ZouhirYachou/RPI5_RGsB_HAT/images/PXL_20260119_183532538.jpg

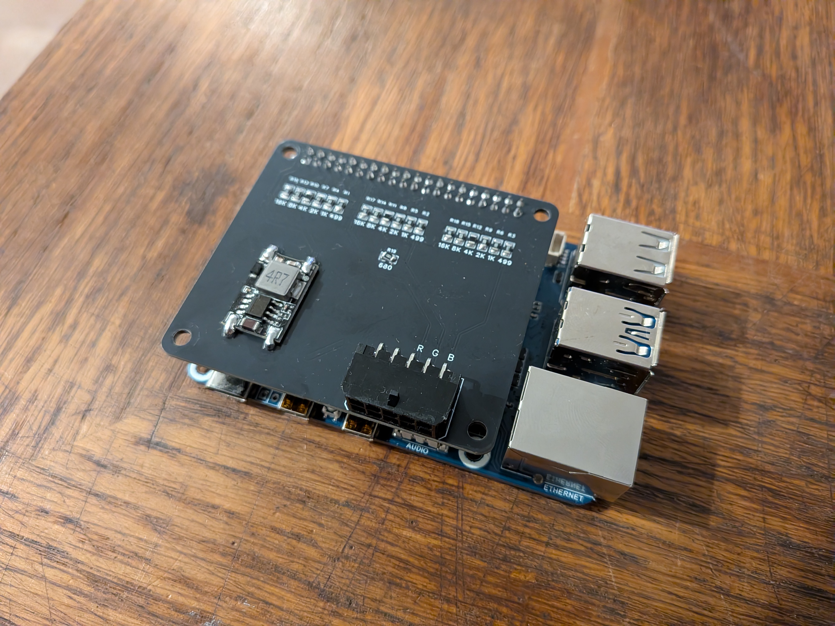
images/PXL_20260119_183532538.jpg
