ZouhirYachou/RPI5_RGsB_HAT/images/PXL_20260119_203551916.jpg

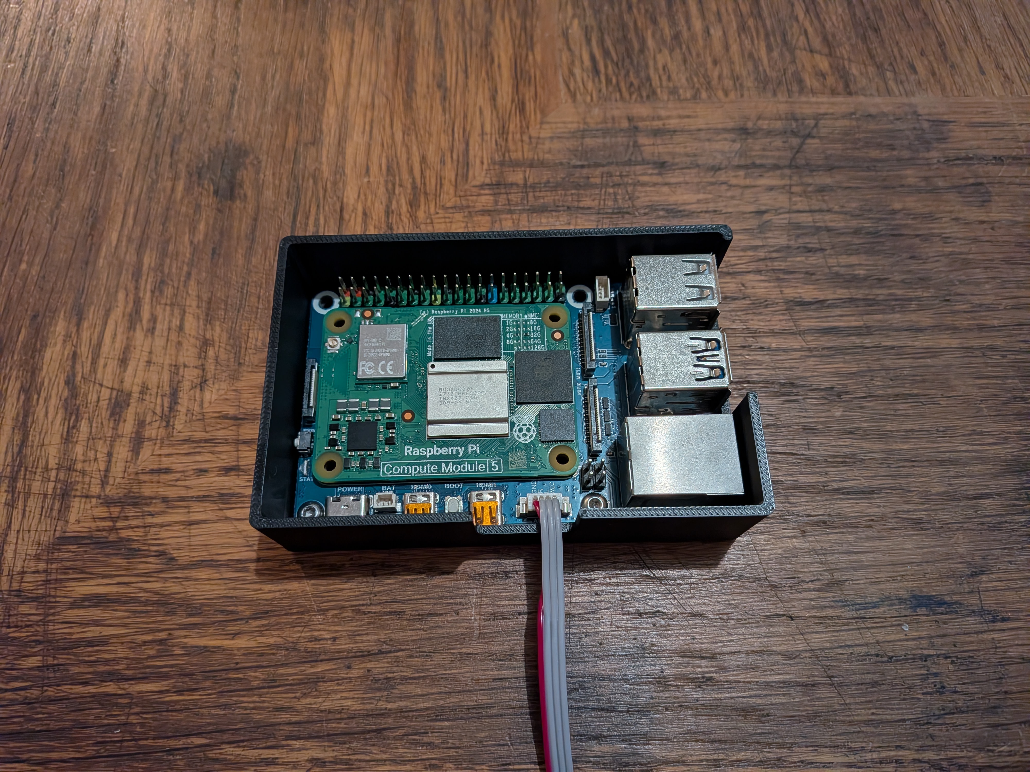
images/PXL_20260119_203551916.jpg
