ZouhirYachou/RPI5_RGsB_HAT/images/PXL_20260119_203603677.jpg

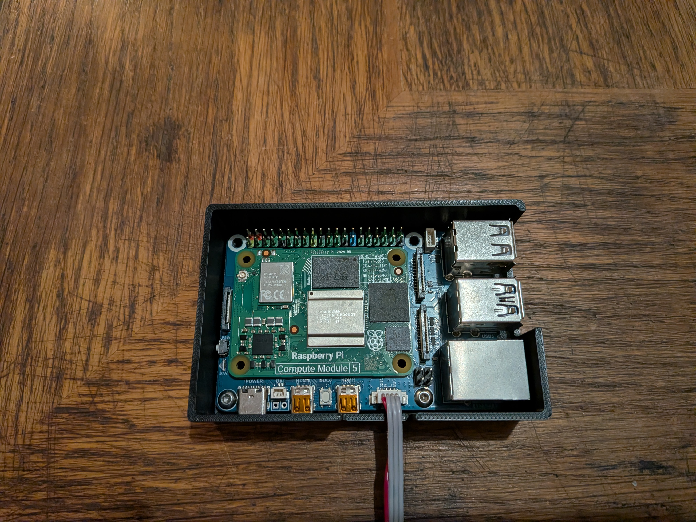
images/PXL_20260119_203603677.jpg
