ZouhirYachou/RPI5_RGsB_HAT/images/PXL_20260119_203711294.jpg

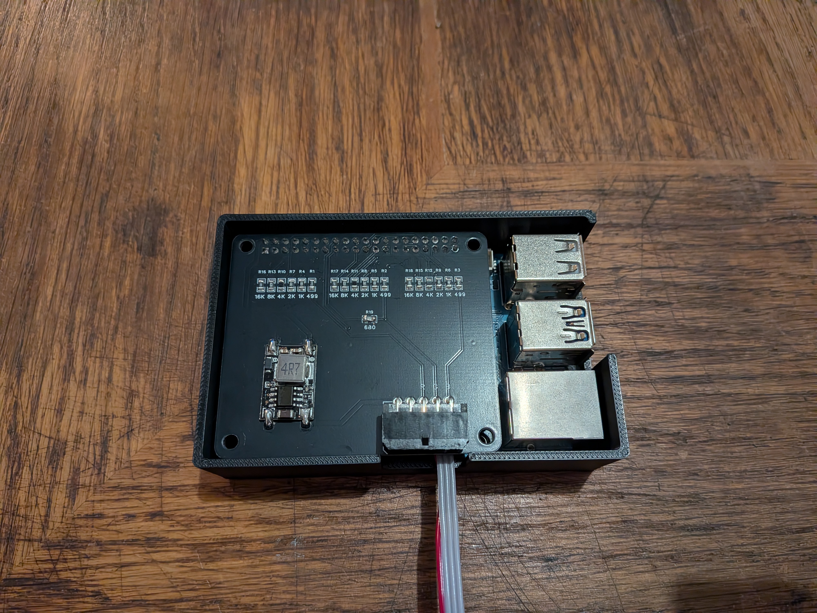
images/PXL_20260119_203711294.jpg
