ZouhirYachou/RPI5_RGsB_HAT/images/PXL_20260119_224216837.jpg

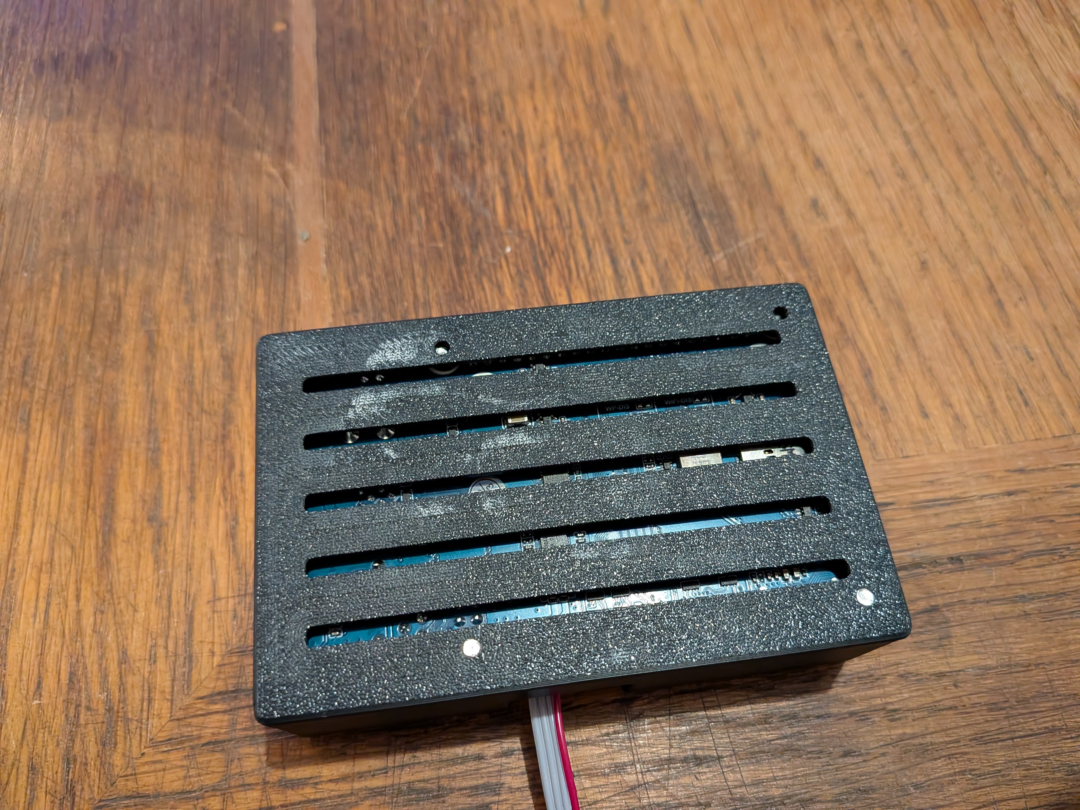
images/PXL_20260119_224216837.jpg
